dabecart/TheAvalancheRoll/Images/DiagramaConexiones.png

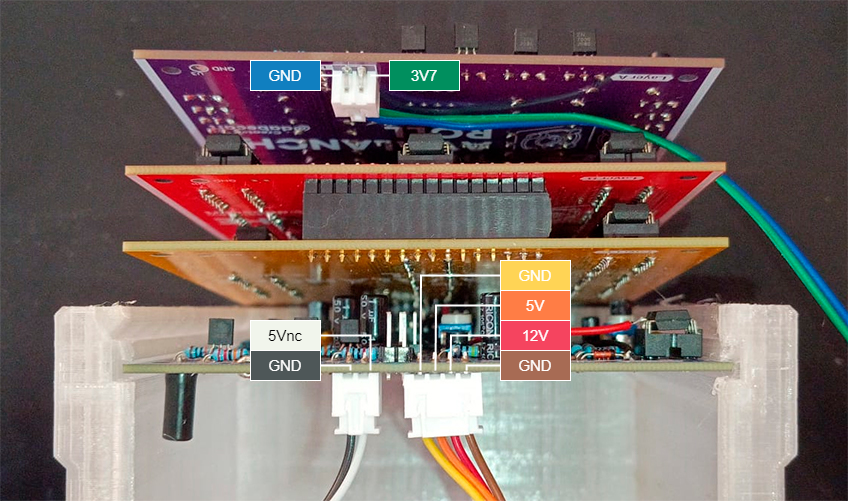
Images/DiagramaConexiones.png
