dabecart/TheAvalancheRoll/Images/DiagramaPower.png

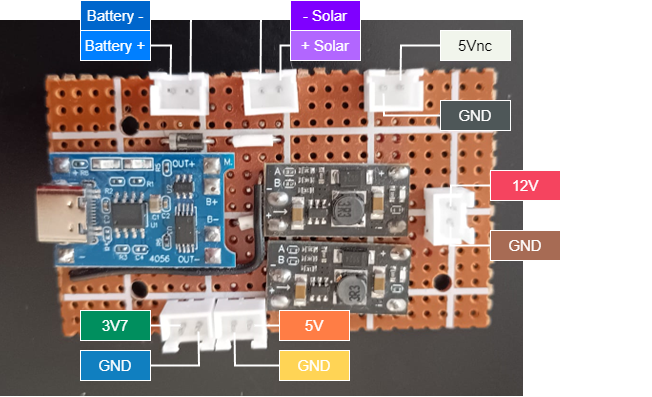
Images/DiagramaPower.png
