dabecart/TheAvalancheRoll/Images/Power.png

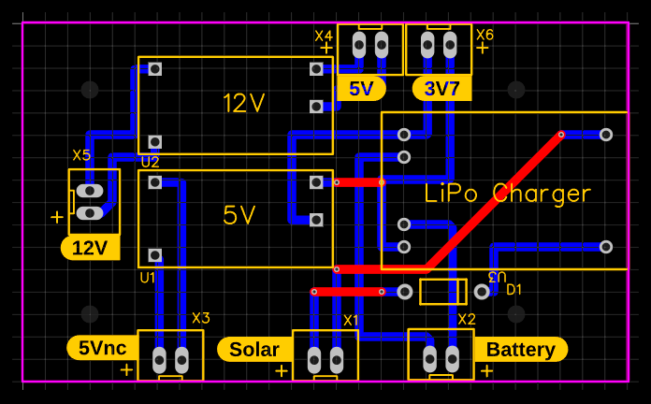
Images/Power.png
