dabecart/TheAvalancheRoll/3d/stl_v2/Dice_v2 - Dice_Front-1.STL

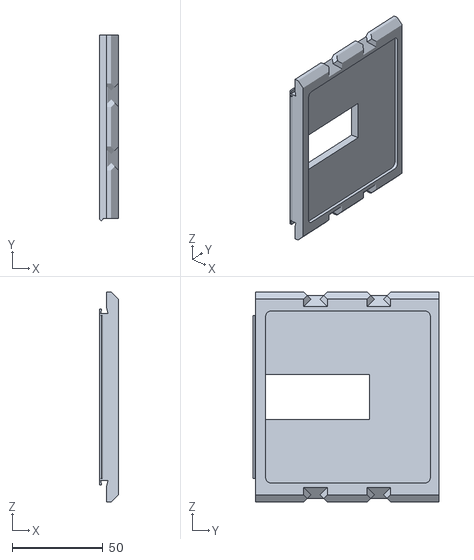
[picture p17: CAD file, 2024-11-10]
3d/stl_v2/Dice_v2 - Dice_Front-1.STL
10.4 x 102.7 x 116.0
