dabecart/TheAvalancheRoll/3d/stl_v2/Dice_v2 - BatteryHolder^Dice_v2-1.STL

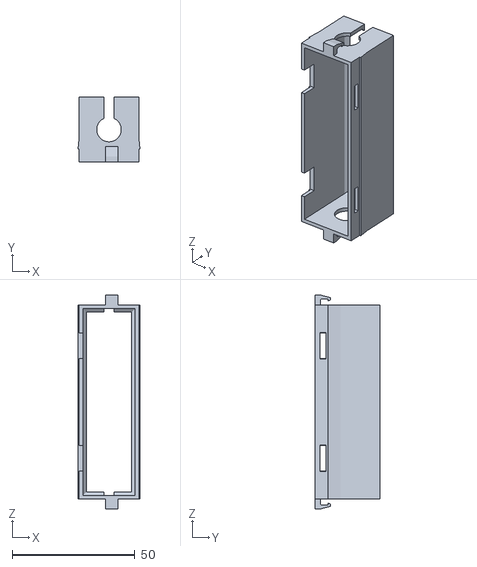
[picture p18: CAD file, 2024-11-10]
3d/stl_v2/Dice_v2 - BatteryHolder^Dice_v2-1.STL
25.3 x 26.5 x 87.3
