dabecart/TheAvalancheRoll/Manual_Renders/render_test/JPEG/Step1.jpg

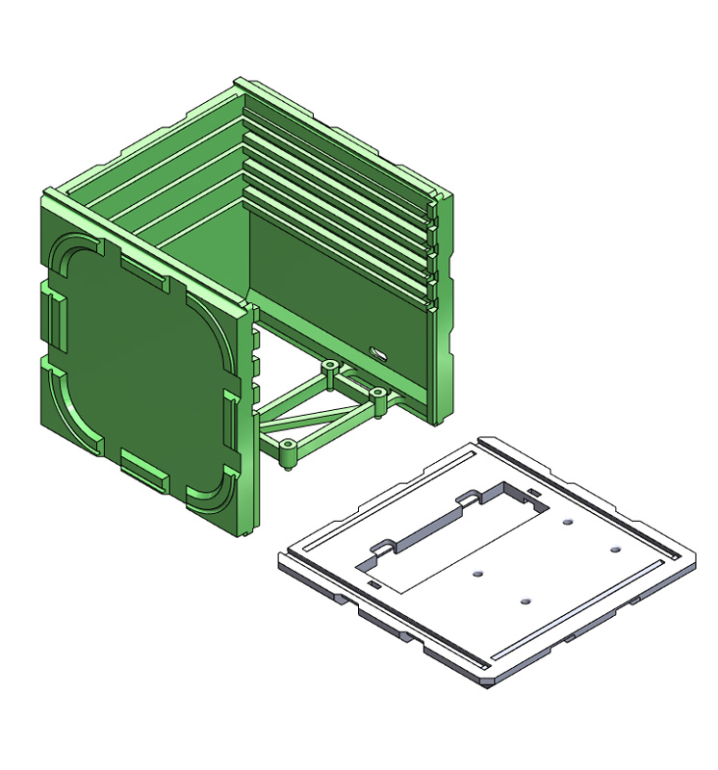
Manual_Renders/render_test/JPEG/Step1.jpg
