dabecart/TheAvalancheRoll/Manual_Renders/render_test/JPEG/Step2.jpg

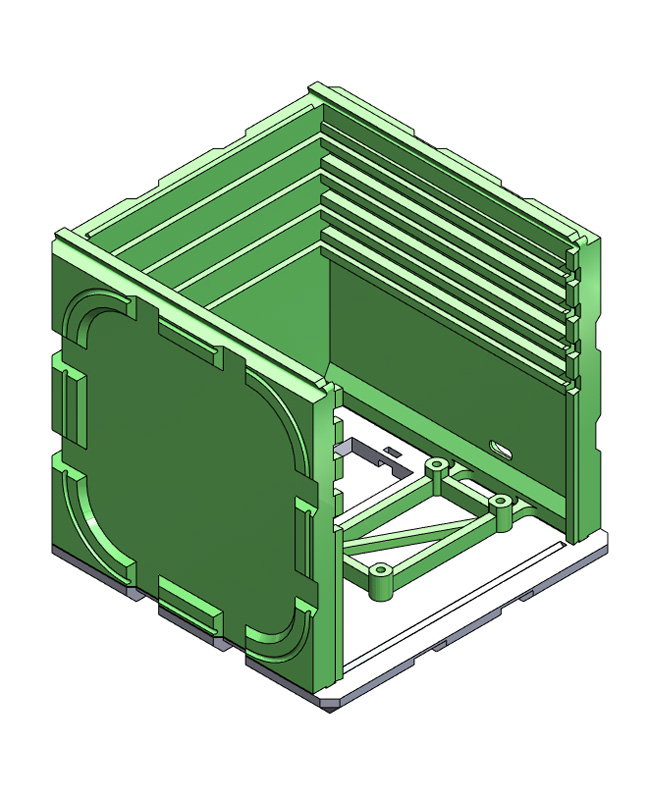
Manual_Renders/render_test/JPEG/Step2.jpg
