dabecart/TheAvalancheRoll/Manual_Renders/render_test/JPEG/Step3.jpg

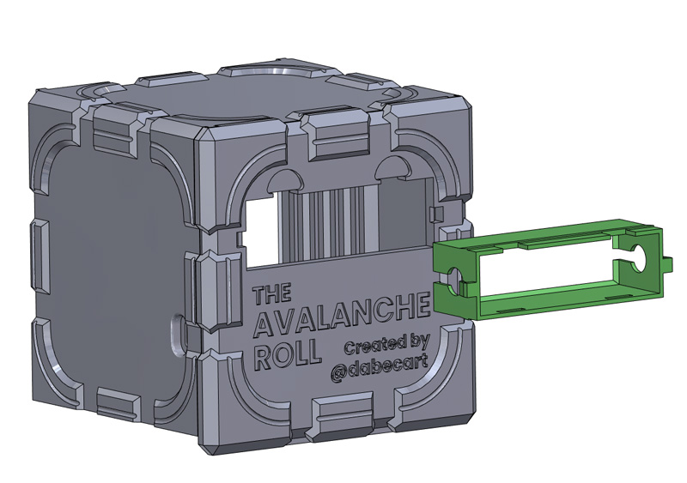
Manual_Renders/render_test/JPEG/Step3.jpg
