dabecart/TheAvalancheRoll/Manual_Renders/render_test/JPEG/Step4.jpg

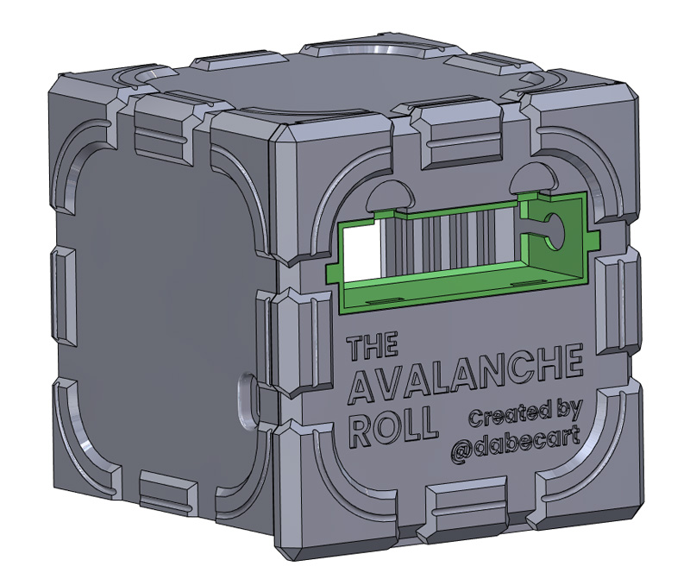
Manual_Renders/render_test/JPEG/Step4.jpg
