dabecart/TheAvalancheRoll/Manual_Renders/render_test/JPEG/Step5.jpg

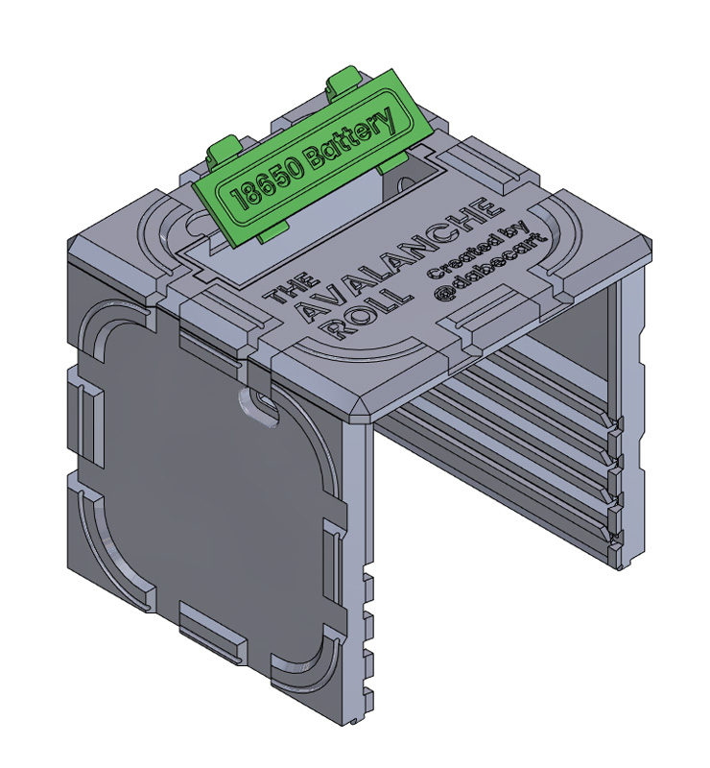
Manual_Renders/render_test/JPEG/Step5.jpg
