dabecart/TheAvalancheRoll/Manual_Renders/render_test/JPEG/Step6.jpg

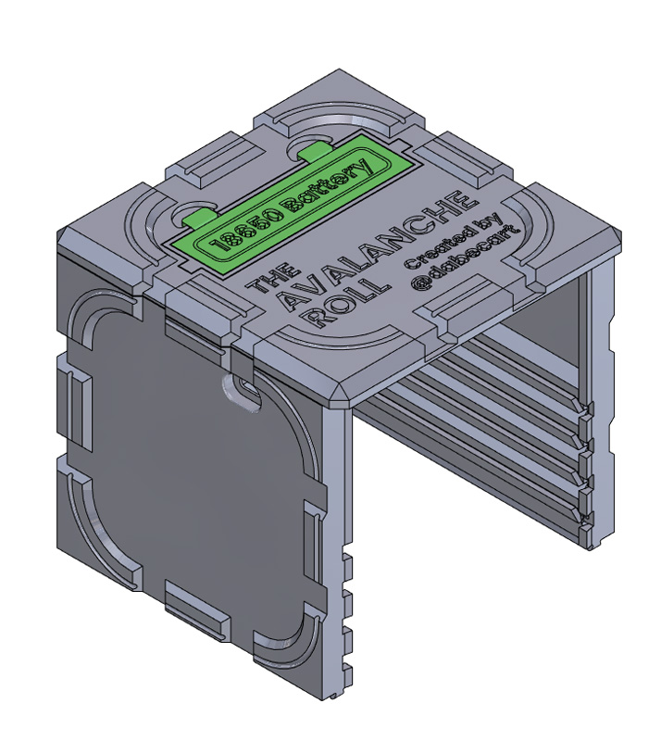
Manual_Renders/render_test/JPEG/Step6.jpg
