dabecart/TheAvalancheRoll/Manual_Renders/render_test/JPEG/Step8.jpg

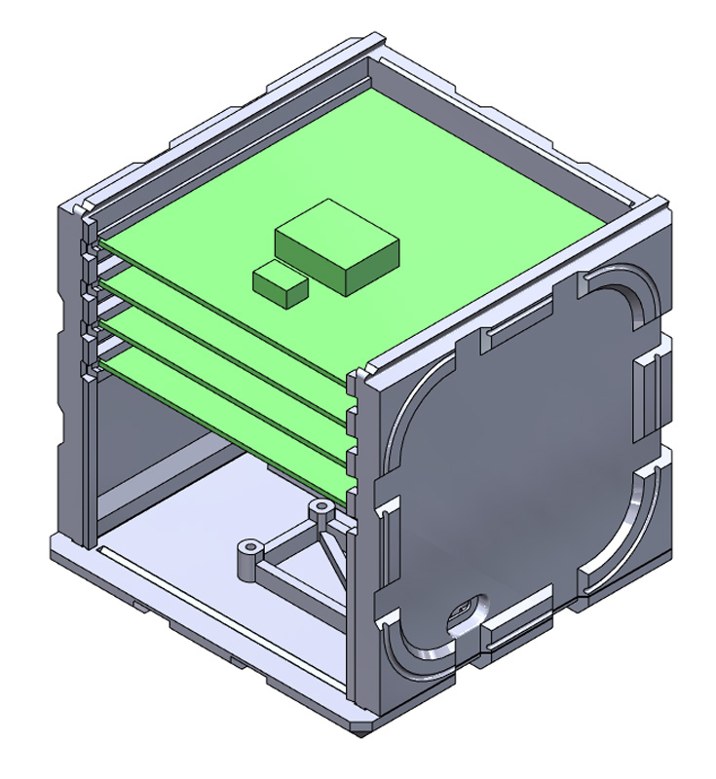
Manual_Renders/render_test/JPEG/Step8.jpg
