dabecart/TheAvalancheRoll/Manual_Renders/render_test/JPEG/Step9.jpg

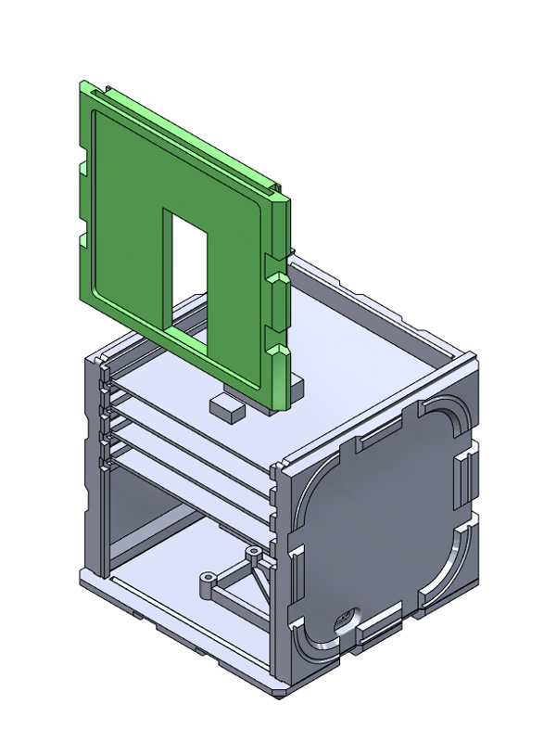
Manual_Renders/render_test/JPEG/Step9.jpg
