dabecart/TheAvalancheRoll/Manual_Renders/render_test/JPEG/Step12.jpg

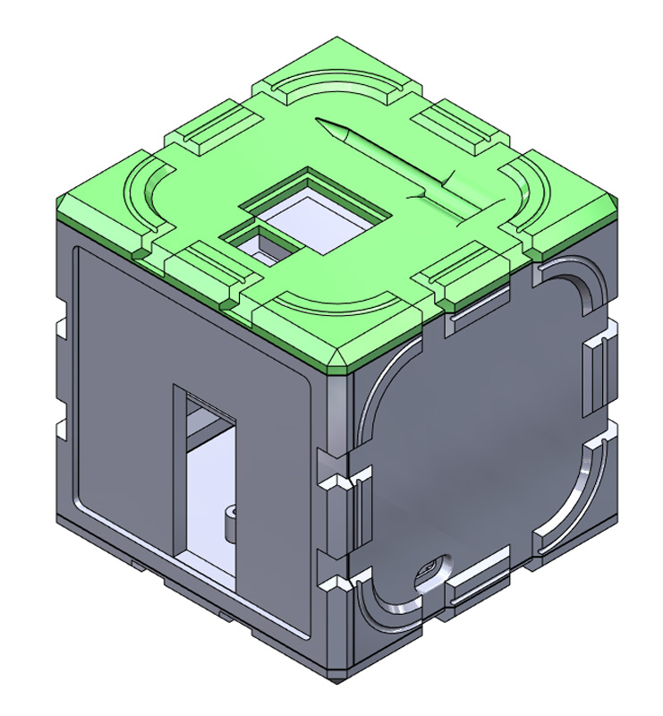
Manual_Renders/render_test/JPEG/Step12.jpg
