dabecart/TheAvalancheRoll/Manual_Renders/render_test/JPEG/Step13.jpg

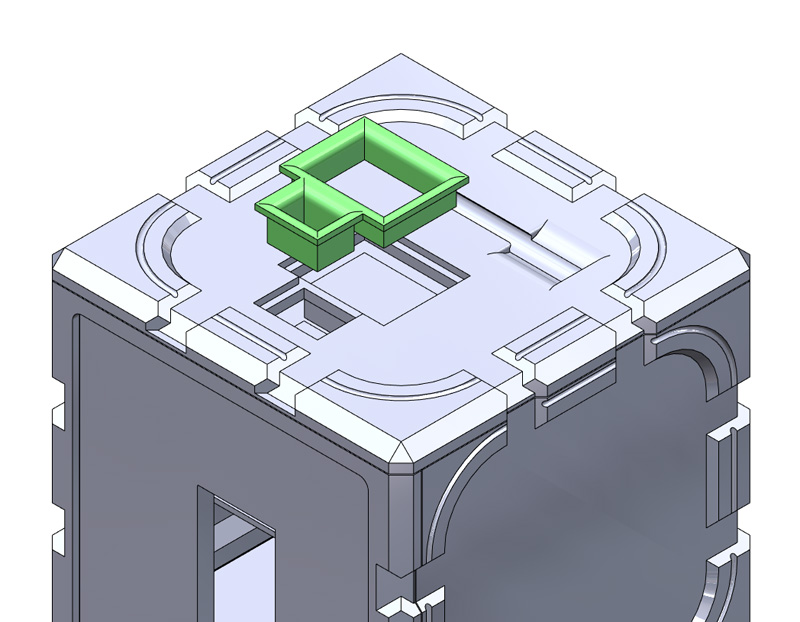
Manual_Renders/render_test/JPEG/Step13.jpg
