dabecart/TheAvalancheRoll/Manual_Renders/render_test/JPEG/Step16.jpg

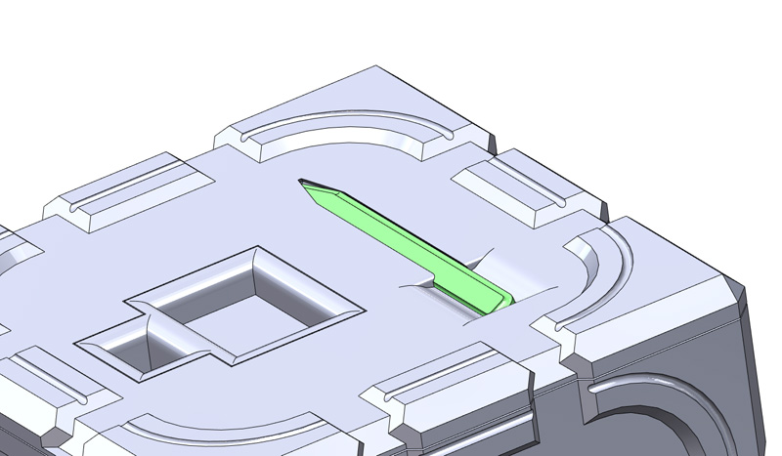
Manual_Renders/render_test/JPEG/Step16.jpg
